orhun/Picasso/usburn/linux/b8.h

/***************************************************************************
 *            b8.h
 *
 *  Wed Aug 23 18:57:43 2006
 *  Copyright  2006  Florian Demski
 *  Copyright  2008  Joerg Bredendiek (sprut)
 *  
 ****************************************************************************/

/*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
 *  You should have received a copy of the GNU General Public License
 *  along with this program; if not, write to the Free Software
 *  Foundation, Inc., 59 Temple Place - Suite 330, Boston, MA 02111-1307, USA.
 */
 
#ifndef __B8_H__
#define __B8_H__


//********************************************************************************************************************
// includes
//********************************************************************************************************************
#include <stdio.h>
#include <string.h>
#include <usb.h>
#include <errno.h>
#include <sys/types.h>
#include <math.h>
#include <string>

#include <stdlib.h>
#include <getopt.h>

using namespace std;

#define byte			__uint8_t
#define word			__uint16_t

#define true			1;
#define false			0;

typedef union _BYTE
{
    byte _byte;
    struct
    {
        unsigned b0:1;
        unsigned b1:1;
        unsigned b2:1;
        unsigned b3:1;
        unsigned b4:1;
        unsigned b5:1;
        unsigned b6:1;
        unsigned b7:1;
    };
} BYTE;


#define SPRUT_VID		0x04D8
#define SPRUT_PID		0xFF0B

#define tietel			"usburn V 0.4 (16.05.2010) by sprut (www.sprut.de)"

#define CMD_READ_VERSION        0x00	/* read programmer id and firmware version */
#define CMD_LED_ONOFF           0x31	/* set LEDs */
#define CMD_RD_ADC              0x37	/* get current ADC value */
#define CMD_SET_AN              0x38	/* select ADC input */
#define CMD_SET_PWM             0x39	/* set pwm value */
#define CMD_SET_SOC             0x3A	/* select socket */
#define CMD_SET_SIGNAL		0x3B	/* set single signals */
#define CMD_SET_DIR		0x3C	/* set direction of PGD */
#define CMD_READ_DATA           0x3D	/* read ICSP data line */
#define CMD_SET_CORE            0x40	/* set PIC family */
#define CMD_SET_PICTYPE         0x41	/* supply information regarding the PIC */
#define CMD_SET_ADDRESS         0x42	/* set address range */
#define CMD_SET_VPP             0x43	/* set Vpp voltage */
#define CMD_READ_EEDATA         0x44	/* read EEPROM of controller PIC */
#define CMD_WRITE_EEDATA        0x45	/* write EEPROM of controller PIC */
#define CMD_READ_CHIPID         0x50	/* read chip id of target */
#define CMD_READ_FLASH          0x51	/* read flash of target */
#define CMD_READ_EEPROM         0x52	/* read EEPROM of target */
#define CMD_READ_IDDATA         0x53	/* read id data of target */
#define CMD_READ_CONFIG         0x54	/* read config data of target */
#define CMD_WRITE_FLASH         0x60	/* write flash of target */
#define CMD_WRITE_EEPROM        0x61	/* write EEPROM of target */
#define CMD_WRITE_IDDATA        0x62	/* write id data of target */
#define CMD_WRITE_CONFIG        0x63	/* write config data of target */
#define CMD_ERASE               0x70	/* erase target */
#define CMD_REMOVECP            0x71	/* remove code protection of target (bulk erase) */
#define CMD_SUPPORTED           0x72    /* ask for supported PIC-families*/
#define CMD_PSUMM          	0x73	/* calculate checksum of mirmware */
#define CMD_RESET               0xFF	/* reset controller PIC */

#define BOOT_READ_VERSION       0x00	/* read programmer id and firmware version */
#define BOOT_READ_FLASH         0x01	/* read flash of controller PIC */
#define BOOT_WRITE_FLASH        0x02	/* write flash of controller PIC */
#define BOOT_ERASE_FLASH        0x03	/* erase flash of controller PIC */
#define BOOT_READ_EEDATA        0x04	/* read EEPROM of controller PIC */
#define BOOT_WRITE_EEDATA       0x05	/* write EEPROM of controller PIC */
#define BOOT_READ_CONFIG        0x06	/* read config data of controller PIC */
#define BOOT_WRITE_CONFIG       0x07	/* write config data of controller PIC */
#define BOOT_RESET              0xFF	/* reset controller PIC */

/* led codes used by CMD_LED_ONOFF */
#define LED1_ON					0x00	/* green */
#define LED1_OFF				0x04	/* green */
#define LED2_ON					0x01	/* yellow */
#define LED2_OFF				0x05	/* yellow */

/* inputs used by CMD_SET_AN */
#define ADC_VPP					0x00
#define ADC_VZ					0x01

/* sockets used by CMD_SET_SOC */
#define SOC_8_14				0x00
#define SOC_18_ICSP				0x01
#define SOC_ICSP				0x01
#define SOC_28_40				0x02
#define SOC_RUN					0xFE
#define SOC_OFF					0xFF

/* signals used by CMD_SET_SIGNAL */
#define SIG_VDD_ON				0x01
#define SIG_VDD_OFF				0x10
#define SIG_VPP_ON				0x02
#define SIG_VPP_OFF				0x20
#define SIG_PGD_ON				0x04
#define SIG_PGD_OFF				0x40
#define SIG_PGC_ON				0x08
#define SIG_PGC_OFF				0x80

/* modes used by CMD_SET_DIR */
#define DIR_PGD_INPUT				0x00
#define DIR_PGD_OUTPUT				0x01

/* cores used by CMD_SET_CORE */
#define CORE_12					12
#define CORE_14					14
#define CORE_16					16
#define CORE_17					17
#define CORE_18					18
#define CORE_30					30
#define	CORE_33					33

#define MODE_NORMAL             0x01	/* programmer in normal mode */
#define MODE_BOOT               0x02	/* programmer in boot loader mode */

#define MODE_INT                0x04	/* usb interface : interrup mode */
#define MODE_BULK               0x08	/* usb interface : bulk mode */

#define	DEVICE_B8		0x00	// Brenner8
#define	DEVICE_BOOT		0x01	// Bootloader
#define	DEVICE_B9		0x03	// Brenner9

#define TIMEOUT_WRITE			100
#define TIMEOUT_READ			1000

#define USB_BLOCKSIZE			64
#define CTRL_EEPROM_SIZE		0x100
#define RES_CALIB_NEEDED		1
#define CALIB_FIRST_TRY			18		/* value used as first estimate */

// Flags
#define f_r	prog.flags1.b0
#define f_w	prog.flags1.b1
#define f_c	prog.flags1.b2
#define f_e	prog.flags1.b3
#define f_p	prog.flags1.b4
#define f_i	prog.flags1.b5
#define f_d	prog.flags1.b6
#define f_l	prog.flags1.b7

#define f_a	prog.flags2.b0
#define f_b	prog.flags2.b1
#define f_o	prog.flags2.b2
#define f_u	prog.flags2.b3
#define f_s	prog.flags2.b4
#define f_h	prog.flags2.b5
#define f_S	prog.flags2.b6
#define f_F	prog.flags2.b7

#define f_n	prog.flags3.b0
#define f_f	prog.flags3.b1
#define f_k	prog.flags3.b2
#define f_t	prog.flags3.b3

// Databasefilenames
#define	P_filename	"picdef03.dat"
#define	C_filename	"cfgdef03.dat"
#define	F_filename	"fildef03.dat"
#define	S_filename	"setdef03.dat"
#define	B_filename	"cekdef03.dat"  //checksum
#define	T_filename	"texdef03.dat"
// max number of datasets in databasefiles
#define	P_filesize	800
#define	C_filesize	6000
#define	F_filesize	20000
#define	S_filesize	60000

// opcodes to put OSCCAL into Flash
#define	MOVLW_12	0x0C00
#define	RETLW_14	0x3400
#define no_OSCCAL	0x1000		// value for no OSCCAL on comandline


class TPIC {
public:
	word	Flash[0x40000];
	word	ROM[0x1000];
	word	ID[8];
	word 	Config[24];
};

typedef struct {     		// 22 Byte
	int	Nr;
	int	Key;
	unsigned int addr;	// 32 bit unsigned
	word	unused;
	int	cfgbitsnr;
	int	fieldNr;
} TCfgbits;

typedef struct {		//25 Byte
	int	Nr;
	int	Key;
	word	mask;
	int	desc;
	byte	flags;		//0:-  1:h  2:xh
	word	init;
	int	fieldNr;
	int	settingNr;
} TField;

typedef struct {		//20 Byte
	int	Nr;
	word	req;
	word	value;
	int	desc; 
	int	settingNr;
	int	checksum;
} TSetting;

typedef struct {		//12 Byte
	int	Nr;
	word	typ;
	word	protstart;
	int	protende;
} TChecksum;



#pragma pack(push, 8)					/* set alignment to 8 -- really important */

//Struktur of the database
typedef struct {
	char name[21];
	__uint8_t cpu;
	__uint8_t power;
	__uint8_t fill1;	//unpacked
	__int32_t config;
	__uint8_t software;
	__uint8_t fill2;	//unpacked
	__uint8_t fill3;	//unpacked
	__uint8_t fill4;	//unpacked
	__int32_t blocksize;
	__uint8_t pins;
	char ExtraStr[17];
	__uint8_t fill5;	//unpacked
	__uint8_t fill6;	//unpacked
	__int32_t ExtraInt;
	__uint8_t ExtraBool;
	
	struct {
		__uint8_t io, adc, adctyp, uart, spi, i2c, can, usb, timer, compare,
			capture, pwm, ccp, eccp, ssp, ext;
		__uint8_t fill7;	//unpacked
		__uint8_t fill8;	//unpacked
		__uint8_t fill9;	//unpacked	
	} interfaces;
	
	struct {
		double min, max, deflt;
	} vpp;
	
	struct {
		double min, max, dfltmin, dfltmax, nominal;
	} vdd;
	
	struct {
		__uint8_t memtech, ovrpgm, tries;
		__uint8_t fill10;	//unpacked
		__uint8_t fill11;	//unpacked
		__uint8_t fill12;	//unpacked
		__uint8_t fill13;	//unpacked
		__uint8_t fill14;	//unpacked
		double lvpthresh;
		__uint16_t panelsize;
		__uint8_t fill15;	//unpacked
		__uint8_t fill16;	//unpacked
		__uint8_t fill17;	//unpacked
		__uint8_t fill18;	//unpacked
		__uint8_t fill19;	//unpacked
		__uint8_t fill20;	//unpacked
	} pgming;
	
	struct {
		__uint16_t pgm, lvpgm, eedata, cfg, userid, erase, lverase;
	} wait;
	
	struct {
		unsigned char pgm, eedata, userid, cfg, rowerase;
		__uint8_t fill21;	//unpacked
	} latches;
	
	struct {
		signed long int min, max;    // 32 Bit mit vorzeichen, klappt so nicht unter 64-bit-Linux
	} pgmmem;
	
	struct {
		signed long int min, max;
	} eedata;

	struct {
		signed long int min, max, modeaddr;
	} extpgm;

	struct {
		signed long int min, max;
	} cfgmem;
	
	struct {
		signed long int min, max;
	} calmem;

	struct {
		signed long int min, max;
	} userid;

	struct {
		__uint32_t min, max;
		__uint16_t idmask, id;
	} devid;
	
	struct {
		__uint8_t flash, eeprom, id, config, erase, cp, read_eeprom;
	} taktik;
	__uint8_t fill21;	//unpacked
	__uint8_t fill22;	//unpacked
	__uint8_t fill23;	//unpacked
	__uint8_t fill24;	//unpacked
	__uint8_t fill25;	//unpacked
	
} TPicDef;



// datastructure for the programmer

typedef struct T_taktik  // 7 Byte
{
	byte	flash;
	byte	eeprom;
	byte	id;
	byte	config;
	byte	erase;
	byte	cp;
	byte	read_eeprom;
} T_taktik;
typedef struct T_latches // Schreibpuffergrößen in Byte
                         // 5 Byte
{
	byte	pgm ;
	byte	eedata;
	byte	userid;
	byte	cfg;
	byte	rowerase;    // Löschbereich
                                                    // in Byte
} T_latches;
typedef struct T_wait    // alle Brenn-Zeiten in Mikrosekunden
                         // 14 Byte
{
	word	pgm;
	word	lvpgm;
	word	eedata;
	word	cfg;
	word	userid;
	word	erase;
	word	lverase;
} T_wait;
typedef struct T_PICtype // 9 + 7 + 5 + 14 = 35 Byte
{
	byte	cpu;
	byte	power;
// 		unsigned int blocksize;
	word	blocksize;
	byte	pins;
	byte	vpp;
	word	panelsize;
	T_taktik	taktik;
	T_latches	latches;
	T_wait		wait;
} T_PICtype;



#pragma pack(pop)

struct programmer {
	usb_dev_handle *dev;
	int interface;
	int ep_in, ep_out;
	int usbmode;
	int mode;
	
	int fw;			// version (e.g. firmwareversion)
	int device;		// device: 0-Brenner8; 1=Bootloader 2=USB4A 3=Brenner9
	char usb_name[64];
	unsigned char supp;
	
	double refZ, divU;
	double gainOff, pwm0VOff, gainOn, pwm0VOn;
	double vdd;
	
	int in_calibration, block_timer;
	char VppLoopMode;	//0-nichts / 1-immer / 2-einmalig / 3- nur herunterregeln
	unsigned char socket, core;

	double d_Uz;		//Referenzspannung Z-Diode
	double d_DIV;		//VppSpannungsteiler
	double d_gain_off;
	double d_pwm0v_off;
	double d_gain_on;
	double d_pwm0v_on;
	double d_Vusb_cal;	// Betriebsspannung bei kalibrierung
	double d_korr;		//Ukor
	float U00_off;
	float U00_on;
	BYTE flags1;
	BYTE flags2;
	BYTE flags3;
	byte ADCL;
	byte ADCH;

	int max_flash;
	int max_ee;
	int EndFlash;
	int EndEE;
	word chipid;
	word revision;
	
	TPicDef pic;		// alles über den PIC fuer den Brenner
	TPIC HexIn, HexOut;
	word Calmem[40000];
	char calmemsaved;
	char InHexfilename[255];
	char OutHexfilename[255];
	char picname[21];
	char OsccalString[10];
	word OsccalRom;
	int OsccalPar;		// OSCCAL-valu from komandline option, cvan be negative vor PIC10F
	word BGmask;
	int BGadr;
	word BGvalue;
	char BGString[10];
	word BGnewvalue;
	byte WRITE_EDATA_KEY;
};

extern struct programmer prog;



#ifdef __cplusplus
extern "C" {
#endif



/* programmer_usb.c */
void sleepms(unsigned int mseconds);
unsigned char d2c(double d);

void init_system(void);
void cleanup_system(void);
int search_brenner8(void);
int programmer_command(unsigned char *data_in, int datasz, unsigned char *data_out);

int prog_get_version(void);
int prog_set_led(unsigned char led);
int prog_get_supported(void);
int prog_read_adc(void);
int prog_set_an(unsigned char an);	
int prog_set_signal(unsigned char signal);
int prog_set_pwm(unsigned char pwm_off, unsigned char pwm_on);
int prog_set_vpp(unsigned char vppl, unsigned char vpph);
int prog_read_eedata(int start, int length, unsigned char *dst);
int prog_write_eedata(int start, unsigned char *src, int length);
int prog_reset(void);
int prog_read_chipid(void);
int prog_set_address(int start, int stop);
int EraseTPIC(TPIC & PIC);
int prog_read_flash(int start, int stop);
int prog_read_calmem(int start, int stop);
int prog_read_ee(int start, int stop);
int prog_read_ID(void);
int prog_read_CONFIG(void);
int prog_check_firmware(void);
int prog_write_flash(int start, int stop);
int prog_write_ee(int start, int stop);
int prog_write_config(void);
int prog_write_id(void);
int prog_erase(void);
int prog_removecp(void);
int prog_set_core(unsigned char core);
int prog_set_pictype(TPicDef& pic);
int prog_set_socket(unsigned char socket);
int prog_target_run(void);
int prog_regulate_vpp(double lower, double mid, double upper);
int prog_identify(unsigned char core, unsigned char socket);
	
	
/* firmware.c */
int firm_boot_on(void);
int firm_upload(void);
int firm_boot_off(void);
	

/* calibration.c */
int cal_step3(void);			// Messung der PWM-Regelsteilheit
int cal_write_data(void);		// write calibration data to control PIC
int cal_read_data(void);		// read calibration data from control PIC

int vpp_loop_on(int mode);
int vpp_loop_off(void);
float cal_Kalibrierespannung(void);
float vpp_getADC(int kanal, int zyklen);
float vpp_getVoltage(int kanal, int Zyklen);
float vpp_getVpp(void);
float vpp_getVpp_stable(void);
int vpp_setVpp(float VppSoll);


/* database.c */
int db_lookup_pic(void);
int db_findpicname(TPicDef& pic);
int db_listpics(__uint8_t software);
int db_findpicid(__uint16_t picid, TPicDef& pic);
int db_load_db(void);
word db_getdefConfMask(int adr);
void db_find_BG(void);


/* hexfile.c */
string hex2str(int zahl);
int idNr(int adr);
int confNr(int adr);
word PICzelle(int adr);	
//word getleerwert(int adr, unsigned char core);
word getleerwert(int adr);
int savehex12(int anfang, int ende);
int savehex14(int anfang, int ende);
int savehex16(int anfang, int ende);
int savehex30(int anfang, int ende);
int SaveHexout12(void);
int SaveHexout14(void);
int SaveHexout16(void);
int SaveHexout30(void);
int savehexout(void);
int openhexfile(void);


/* testc */
int test_hardware(void);


#ifdef __cplusplus
}
#endif

#endif /* __B8_H__ */
